TharushaNimesh22/AnalogProject/LatexResources/with PCBs.png

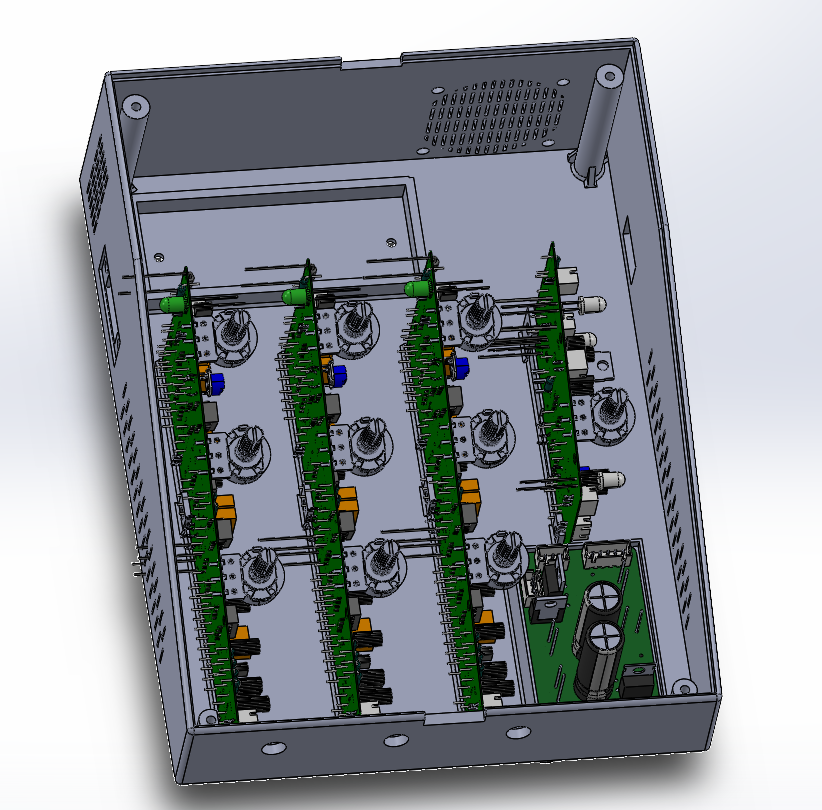
LatexResources/with PCBs.png
