TharushaNimesh22/AnalogProject/Simulation/TL072_Equalizer_zelenkey.asc

C1: cap; 100nF
C2: cap; 100nF
C3: cap; 10nF
C4: cap; 10nF
C5: cap; 100nF
C6: cap; 100nF
C7: cap; 10nF
C8: cap; 10nF
C9: cap; 100nF
C10: cap; 100nF
C11: cap; 10nF
C12: cap; 10nF
R1: res; 6.2K
R2: res; 6.2K
R3: res; 1000
R4: res; 5000
R5: res; 470
R6: res; 470
R7: res; 470
R8: res; 470
R9: res; 470
R10: res; 470
R11: res; 470
R12: res; 3.9K
R13: res; 3.9K
R14: res; 1000
R15: res; 5000
R16: res; 6.2K
R17: res; 6.2K
R18: res; 3.9K
R19: res; 3.9K
R20: res; 1000
R21: res; 5000
R22: res; 22K
R23: res; 22K
R24: res; 22K
R25: res; 22K
R26: res; 32K
R27: res; 32K
R28: res; 820
R29: res; 820
U1: TL072
U2: TL072
U3: TL072
U4: TL072
U5: TL072
U6: TL072
U7: TL072
U8: TL072
U9: TL072
U10: TL072
U11: TL072
U12: TL072
U13: TL072
V1: voltage; SINE(0 60mV 3000)
V2: voltage; SINE(0 20mV 1000)
V3: voltage; SINE(0 30mV 150)
V4: voltage; SINE(0 50mV 50)
V5: voltage; SINE(0 30mV 4500)
V6: voltage; SINE(0 50mV 6000); AC 1
V7: voltage; 12
V8: voltage; -12
Named nets: 0, V+, V-
.tran 0 100ms 0ms 0.1ms
Signal Generator 1
Low pass filter
Amplifier
Low Ferequency Band  50Hz - 250Hz
Low pass filter
Amplifier
Mid Ferequency Band  250Hz - 4kHz
High pass filter
High pass filter
Amplifier
High Ferequency Band  4kHz - 20kHz
Input Buffer
3 Channel Equalizer
Output Buffer
Frequency Band Mixer
.ac dec 100 10 100k
High pass filter
Low pass filter
